profdc9/PicoParanoia/Code/src/fileenc.cpp

/*
 * Copyright (c) 2020 Daniel Marks

This software is provided 'as-is', without any express or implied
warranty. In no event will the authors be held liable for any damages
arising from the use of this software.

Permission is granted to anyone to use this software for any purpose,
including commercial applications, and to alter it and redistribute it
freely, subject to the following restrictions:

1. The origin of this software must not be misrepresented; you must not
   claim that you wrote the original software. If you use this software
   in a product, an acknowledgment in the product documentation would be
   appreciated but is not required.
2. Altered source versions must be plainly marked as such, and must not be
   misrepresented as being the original software.
3. This notice may not be removed or altered from any source distribution.
 */

#include <stdlib.h>
#include <string.h>
#include <stdint.h>
#include <ff.h>
#include <ChaChaPoly.h>
#include "consoleio.h"
#include "fileop.h"
#include "fileenc.h"
#include "keymanager.h"
#include "cryptotool.h"
#include "random.h"

#ifdef __cplusplus
extern "C" {
#endif

int fileenc_check_key_selected(void)
{
  if (current_key_private.entry_type == KEY_TYPE_SYMMETRIC) return 1;
  if (current_key_private.entry_type == KEY_TYPE_ECDH_PRIVATE)
  {
    if (current_key_public.entry_type == KEY_TYPE_ECDH_PUBLIC) return 1;
      else
    {
      file_report_error("No public key selected");
      return 0;
    }
  }
  file_report_error("No private or symmetric key selected");
  return 0;
}

#define FILEENC_READBUF_SIZE (SYMMETRIC_BLOCKLEN*64)

#define FILEENC_WRITEBUF_SIZE 36

// ChaChaPoly::ivSize() returns 8 (the original 64-bit-nonce ChaCha variant),
// not the RFC 8439 96-bit nonce this codebase uses everywhere else -- see
// cryptotool.cpp / third_party/crypto/PROVENANCE.md. This file instantiates
// ChaChaPoly directly (streaming payload cipher, bypassing symmetric_memcrypt)
// so it needs the same explicit wire length.
#define SYMMETRIC_IV_WIRE_LEN 12

typedef struct _fileenc_readbuf
{
  ChaChaPoly *read_cipher;
  FIL read_file;
  uint8_t  read_buf[FILEENC_READBUF_SIZE];
  uint16_t read_filled;
  uint16_t read_curpos;
  FSIZE_t read_progress;
  FIL write_file;
  uint8_t  write_buf[FILEENC_WRITEBUF_SIZE];
  uint16_t write_curpos;  
  fileenc_total_header fth;
} fileenc_state;

int fileenc_base64_readdata(void *v)
{
  fileenc_state *fr = (fileenc_state *)v;
  if (fr->read_curpos >= fr->read_filled)
  {
    UINT br;
    FRESULT res = f_read(&fr->read_file,fr->read_buf,FILEENC_READBUF_SIZE,&br);
    if ((res != FR_OK) || (br == 0)) return -1;
    fr->read_cipher->encrypt(fr->read_buf, fr->read_buf, br);
    fr->read_filled = br;
    fr->read_curpos = 0;
    if ((f_tell(&fr->read_file)-fr->read_progress) >= FILEENC_DISPLAY_INCREMENT)
    {
      console_puts("Reading ");
      console_printuint(f_tell(&fr->read_file));
      console_putch('/');
      console_printuint(f_size(&fr->read_file));
      console_printcrlf();
      fr->read_progress = f_tell(&fr->read_file);
    }
  }
  return fr->read_buf[fr->read_curpos++];
}

int fileenc_base64_writedata(int c, void *v)
{
  fileenc_state *fw = (fileenc_state *)v;

  if (c >= 0)
    fw->write_buf[fw->write_curpos++] = c; 
  if ((fw->write_curpos == FILEENC_WRITEBUF_SIZE) || (c < 0))
  {
    UINT br;
    f_write(&fw->write_file,fw->write_buf,fw->write_curpos,&br);
    f_write(&fw->write_file,"\n",1,&br);
    fw->write_curpos = 0;
  }
  return 0;   // PicoParanoia fix: the ParanoiaBox original omits this return.
              // Same class of bug as fileblockencode_writedata (see fileop.cpp):
              // the caller, base64_encode, ignores the value, but a missing
              // return in a non-void function is UB that HardFaults on this
              // toolchain/target. Caught by -Werror=return-type.
}

const char *fileenc_filename(const char *c)
{
  const char *d = &c[strlen_n(c)];
  while (d>c)
  {
    d--;
    if ((*d == '/') || (*d == ':')) return (d+1);
  }
  return d;
}

void fileenc_encrypt_state(fileenc_state *fs)
{
  char filename_plaintext[256];
  if (!fileenc_check_key_selected()) return;
  {
    char filename_ciphertext[256];
    if (!file_select_plaintext("Select plaintext file", 0, filename_plaintext, sizeof(filename_plaintext)-1)) return;
    if (!file_select_ciphertext("Select directory for ciphertext", 1, filename_ciphertext, sizeof(filename_ciphertext)-1)) return;
    if (!file_enter_filename("Filename for ciphertext output:", filename_ciphertext, sizeof(filename_ciphertext)-1)) return;
    FRESULT fres;
    fres = f_open(&fs->read_file, filename_plaintext, FA_READ);
    if (fres != FR_OK)
    {
      file_report_error("Could not open plaintext file");
      return;
    }
    fres = f_open(&fs->write_file, filename_ciphertext, FA_WRITE | FA_CREATE_NEW);
    if (fres != FR_OK)
    {
      file_report_error("Could not create ciphertext file");
      f_close(&fs->read_file);
      return;    
    }
  }
  console_clrscr();
  console_puts("Encrypting file:\r\n");
  {
    uint8_t secret[KEYMANAGER_MAX_SECRET_LEN];
    uint8_t tag[SYMMETRIC_TAGLEN];
    int secretlen = sizeof(secret);
    uint8_t key_success = 0;

    ChaChaPoly read_cipher;
    uint8_t salt2[KEYMANAGER_HASHLEN];
    uint8_t iv2[SYMMETRIC_IVLEN];
    uint8_t key1[SYMMETRIC_KEYLEN];
    uint8_t key2[SYMMETRIC_KEYLEN];

    memset((void *)&fs->fth,'\000',sizeof(fs->fth));
    randomness_get_whitened_bits(fs->fth.iv1, sizeof(fs->fth.iv1));
    randomness_get_whitened_bits(fs->fth.salt1, sizeof(fs->fth.salt1));
    randomness_get_whitened_bits(salt2, sizeof(salt2));
    randomness_get_whitened_bits(iv2, sizeof(iv2));
 
    if (keymanager_get_symmetric_key(secret, &secretlen))
    {
       randomness_get_whitened_bits(fs->fth.ephemeral_public_key,sizeof(fs->fth.ephemeral_public_key));
       key_success = 1;
    }
    else
    {
       uint8_t ephemeral_private_key[KEYMANAGER_PRIVATEKEY_LEN];
       fileenc_secret_concatenation shared_secrets;
       keymanager_create_ephemeral_key(fs->fth.ephemeral_public_key,sizeof(fs->fth.ephemeral_public_key),
                                       ephemeral_private_key,sizeof(ephemeral_private_key));
       key_success = keymanager_shared_secrets_with_public_key(
          shared_secrets.shared_secret_ephemeral,shared_secrets.shared_secret_private,ephemeral_private_key);
       ctblake2s(secret, secretlen, (const void *)&shared_secrets, sizeof(shared_secrets), NULL, 0);
       memset((void *)&shared_secrets,'\000',sizeof(shared_secrets));
       memset((void *)&ephemeral_private_key,'\000',sizeof(ephemeral_private_key));
    }

    if (key_success)
    {
      key_derivation_function((void *)key1, secret, secretlen, fs->fth.salt1, sizeof(fs->fth.salt1));
      fs->fth.fhpu.fhp.id   =         FILEENC_EXPORT_ID;
      fs->fth.fhpu.fhp.entry_type =   current_key_private.entry_type;
      fs->fth.fhpu.fhp.vers =         FILEENC_EXPORT_VERSION;
      fs->fth.fhpu.fhp.len =          sizeof(fs->fth.fhpu.fhp);
      fs->fth.fhpu.fhp.totallen =     sizeof(fs->fth.fhpu);
      fs->fth.fhpu.fhp.file_length =  f_size(&fs->read_file);
      memcpy((void *)fs->fth.fhpu.fhp.salt2, (void *)salt2, sizeof(fs->fth.fhpu.fhp.salt2));
      memcpy((void *)fs->fth.fhpu.fhp.iv2, (void *)iv2, sizeof(fs->fth.fhpu.fhp.iv2));
      strcpy_n(fs->fth.fhpu.fhp.filename, fileenc_filename(filename_plaintext), sizeof(fs->fth.fhpu.fhp.filename)-1);
      symmetric_memcrypt(1, (void *)key1, (void *)fs->fth.iv1, (void *)fs->fth.tag1, (void *)&fs->fth.fhpu, sizeof(fs->fth.fhpu));
      file_write_block(&fs->write_file, "PARANOIABOX-FILEHEADER", (void *)&fs->fth, sizeof(fs->fth));

      file_write_header(&fs->write_file,"PARANOIABOX-PAYLOAD",0);
      fs->read_cipher = &read_cipher;
      fs->read_filled = fs->read_curpos = 0;
      fs->write_curpos = 0;
      fs->read_progress = 0;
      key_derivation_function((void *)key2, secret, secretlen, salt2, sizeof(salt2));
      fs->read_cipher->setKey((const uint8_t *)key2, fs->read_cipher->keySize());
      fs->read_cipher->setIV((const uint8_t *)iv2, SYMMETRIC_IV_WIRE_LEN);
      base64_encode(fileenc_base64_readdata,(void *)fs,  fileenc_base64_writedata, (void *)fs);
      fileenc_base64_writedata(-1, (void *)fs);
      fs->read_cipher->computeTag((uint8_t *)tag, SYMMETRIC_TAGLEN);
      file_write_header(&fs->write_file,"PARANOIABOX-PAYLOAD",1);
      
      file_write_block(&fs->write_file, "PARANOIABOX-ENDBLOCK", (void *)tag, sizeof(tag));      
    } else file_report_error("Bad secret key");
    memset((void *)&secret,'\000',sizeof(secret));
  }  
  f_close(&fs->write_file);
  f_close(&fs->read_file);
}

void fileenc_encrypt(void)
{
  fileenc_state *fs = (fileenc_state *)malloc(sizeof(fileenc_state));
  if (fs == NULL) return;
  fileenc_encrypt_state(fs);
  free(fs);
}


#define FILEDEC_READBUF_SIZE 512

#define FILEDEC_WRITEBUF_SIZE (SYMMETRIC_BLOCKLEN*64)

typedef struct _filedec_readbuf
{
  FIL          read_file;
  FSIZE_t      read_last_block;
  uint8_t      read_buf[FILEDEC_READBUF_SIZE];
  uint16_t     read_filled;
  uint16_t     read_curpos;
  uint8_t      read_abort;
  FIL          write_file;
  uint8_t      write_buf[FILEDEC_WRITEBUF_SIZE];
  uint16_t     write_curpos; 
  FSIZE_t      write_progress;
  FSIZE_t      write_total;
  ChaChaPoly  *write_cipher;
  fileenc_total_header fth;
} filedec_state;

int filedec_base64_readdata(void *v)
{
  filedec_state *fr = (filedec_state *)v;
  for (;;)
  {
    if (fr->read_curpos >= fr->read_filled)
    {
      UINT br;
      fr->read_last_block = f_tell(&fr->read_file);
      FRESULT res = f_read(&fr->read_file,fr->read_buf,FILEDEC_READBUF_SIZE,&br);
      if ((res != FR_OK) || (br == 0)) return -1;
      fr->read_filled = br;
      fr->read_curpos = 0;
    }
    uint8_t ch = fr->read_buf[fr->read_curpos++];
    if ((ch == '-') || (fr->read_abort))
    {
      f_lseek(&fr->read_file, fr->read_last_block);
      return -1;
    }
    if (is_base64_char(ch)) return ch;
  }
}

int filedec_base64_writedata(int c, void *v)
{
  filedec_state *fw = (filedec_state *)v;

  if (c >= 0) 
    fw->write_buf[fw->write_curpos++] = c; 
  if ((fw->write_curpos == FILEDEC_WRITEBUF_SIZE) || (c < 0))
  {
    UINT br;
    fw->write_cipher->decrypt(fw->write_buf, fw->write_buf, fw->write_curpos);
    f_write(&fw->write_file,fw->write_buf,fw->write_curpos,&br);
    fw->write_curpos = 0;
    if ((f_tell(&fw->write_file)-fw->write_progress) >= FILEENC_DISPLAY_INCREMENT)
    {
      console_puts("Writing ");
      console_printuint(fw->write_progress);
      console_putch('/');
      console_printuint(fw->write_total);
      console_printcrlf();
      fw->write_progress = f_tell(&fw->write_file);
      if (fw->write_progress > fw->fth.fhpu.fhp.file_length)
        fw->read_abort = 1;
    }
  }
  return 0;
}

void fileenc_decrypt_state(filedec_state *fs)
{
  FSIZE_t destroy_output = 0;
  if (!fileenc_check_key_selected()) return;
  {
    char filename_ciphertext[256];
    char filename_plaintext[256];
    if (!file_select_ciphertext("Select ciphertext file", 0, filename_ciphertext, sizeof(filename_ciphertext)-1)) return;
    if (!file_select_plaintext("Select directory for plaintext", 1, filename_plaintext, sizeof(filename_plaintext)-1)) return;
    if (!file_enter_filename("Filename for plaintext output:", filename_plaintext, sizeof(filename_plaintext)-1)) return;
    FRESULT fres;
    fres = f_open(&fs->read_file, filename_ciphertext, FA_READ);
    if (fres != FR_OK)
    {
      file_report_error("Could not open ciphertext file");
      return;
    }
    fres = f_open(&fs->write_file, filename_plaintext, FA_WRITE | FA_CREATE_NEW);
    if (fres != FR_OK)
    {
      file_report_error("Could not create plaintext file");
      f_close(&fs->read_file);
      return;    
    } 
  }
  console_clrscr();
  console_puts("Decrypting file:\r\n");
  {
    uint8_t secret[KEYMANAGER_MAX_SECRET_LEN];
    int secretlen = sizeof(secret);
    uint8_t key_success = 0;

    memset((void *)&fs->fth,'\000',sizeof(fs->fth));
      
    if(file_read_block(&fs->read_file, "PARANOIABOX-FILEHEADER", (void *)&fs->fth, sizeof(fs->fth)))
    {
      uint8_t key1[SYMMETRIC_KEYLEN];

    if (keymanager_get_symmetric_key(secret, &secretlen))
       key_success = 1;
    else
    {
       fileenc_secret_concatenation shared_secrets;
       key_success = keymanager_shared_secrets_with_private_key(
          shared_secrets.shared_secret_ephemeral,shared_secrets.shared_secret_private,fs->fth.ephemeral_public_key);
       ctblake2s(secret, secretlen, (const void *)&shared_secrets, sizeof(shared_secrets), NULL, 0);
       memset((void *)&shared_secrets,'\000',sizeof(shared_secrets));
    }
    
     if (key_success)
     {
        key_derivation_function((void *)key1, secret, secretlen, fs->fth.salt1, sizeof(fs->fth.salt1));
        if (symmetric_memcrypt(0, (void *)key1, (void *)fs->fth.iv1, (void *)fs->fth.tag1, (void *)&fs->fth.fhpu, sizeof(fs->fth.fhpu)))
        {
           if ((fs->fth.fhpu.fhp.id == FILEENC_EXPORT_ID) && (fs->fth.fhpu.fhp.vers == FILEENC_EXPORT_VERSION) &&
               (fs->fth.fhpu.fhp.len == sizeof(fs->fth.fhpu.fhp)) && (fs->fth.fhpu.fhp.entry_type == current_key_private.entry_type))
           {
              fs->fth.fhpu.fhp.filename[sizeof(fs->fth.fhpu.fhp.filename)-1] = '\000';
              if (file_skip_header(&fs->read_file,"PARANOIABOX-PAYLOAD",0))
              {
                ChaChaPoly  write_cipher;
                uint8_t key2[SYMMETRIC_KEYLEN];
                key_derivation_function((void *)key2, secret, secretlen, fs->fth.fhpu.fhp.salt2, sizeof(fs->fth.fhpu.fhp.salt2));
                fs->write_cipher = &write_cipher;
                fs->read_filled = fs->read_curpos = 0;
                fs->read_abort = 0;
                fs->write_curpos = 0;
                fs->write_progress = 0;
                fs->write_total = fs->fth.fhpu.fhp.file_length;
                fs->write_cipher->setKey((const uint8_t *)key2, fs->write_cipher->keySize());
                fs->write_cipher->setIV((const uint8_t *)fs->fth.fhpu.fhp.iv2, SYMMETRIC_IV_WIRE_LEN);
                base64_decode(filedec_base64_readdata,(void *)fs,  filedec_base64_writedata, (void *)fs);
                filedec_base64_writedata(-1, (void *)fs);
                if (f_tell(&fs->write_file) == fs->fth.fhpu.fhp.file_length)
                {
                  if (file_skip_header(&fs->read_file,"PARANOIABOX-PAYLOAD",1))
                  {
                    uint8_t tag[SYMMETRIC_TAGLEN];
                    if(file_read_block(&fs->read_file, "PARANOIABOX-ENDBLOCK", (void *)tag, sizeof(tag)))
                    {
                      if (fs->write_cipher->checkTag(tag, SYMMETRIC_TAGLEN))
                      {
                         destroy_output = fs->fth.fhpu.fhp.file_length;
                      }
                      else file_report_error("Payload Tag is invalid");
                    } else file_report_error("End block not found");
                  } else file_report_error("End of payload not found");                
                } else file_report_error("Payload length does not match header");
              } else file_report_error("No payload found");
           } else file_report_error("Wrong version of header");
        } else file_report_error("Header Tag is invalid");
      } else file_report_error("Could not read file header");
    } else file_report_error("Bad secret key");
    memset((void *)&secret,'\000',sizeof(secret));
  }
  f_lseek(&fs->write_file,destroy_output);
  f_truncate(&fs->write_file);
  f_close(&fs->write_file);
  f_close(&fs->read_file);
}

void fileenc_decrypt(void)
{
  filedec_state *fs = (filedec_state *)malloc(sizeof(filedec_state));
  if (fs == NULL) return;
  fileenc_decrypt_state(fs);
  free(fs);
}

#ifdef __cplusplus
}
#endif  
