profdc9/PicoParanoia/Code/src/TNTSCAnsi.cpp

/* 
  Copyright (C) 2007 by Daniel Marks

  This software is provided 'as-is', without any express or implied
  warranty.  In no event will the authors be held liable for any damages
  arising from the use of this software.

  Permission is granted to anyone to use this software for any purpose,
  including commercial applications, and to alter it and redistribute it
  freely, subject to the following restrictions:

  1. The origin of this software must not be misrepresented; you must not
     claim that you wrote the original software. If you use this software
     in a product, an acknowledgment in the product documentation would be
     appreciated but is not required.
  2. Altered source versions must be plainly marked as such, and must not be
     misrepresented as being the original software.
  3. This notice may not be removed or altered from any source distribution.
  
  Daniel L. Marks profdc9@gmail.com

*/

#include <stdio.h>
#include <stdlib.h>

#include "TNTSCAnsi.h"

#define STRICT_VT100

#define memmove vidmemmove

static void *vidmemmove(void *s1, const void *s2, size_t n)
{
	unsigned char *ss1 = (unsigned char *)s1;
	const unsigned char *ss2 = (const unsigned char *)s2;
	if (ss1 > ss2) {
		ss1 += n;
		ss2 += n;
		while (n-- > 0) *(--ss1) = *(--ss2);
	} else {
		while (n-- > 0) *ss1++ = *ss2++;
	}
	return s1;
}

// Optional per-cell change hook. A host project can define
// TNTSCANSI_CELL_CHANGED(cur, index, ch) (via the auto-included tntscansi_hook.h)
// to be notified with the linear buffer index whenever a cell changes value, so
// it can blit just that cell. Default is a no-op, which keeps this file a
// standalone VT100 text-buffer emulator with unchanged behavior.
#if defined(__has_include)
#  if __has_include("tntscansi_hook.h")
#    include "tntscansi_hook.h"
#  endif
#endif
#ifndef TNTSCANSI_CELL_CHANGED
#define TNTSCANSI_CELL_CHANGED(cur, index, ch) ((void)0)
#endif

// Optional whole-region clear hook. clear_region() fires this once for the
// whole span instead of the per-cell hook, so a host can do one fast solid
// fill (e.g. pico_ntsc_clear_span) instead of one glyph-blit per cell. Default
// is a no-op.
#ifndef TNTSCANSI_REGION_CLEARED
#define TNTSCANSI_REGION_CLEARED(cur, y1, x1, y2, x2, reverse) ((void)0)
#endif

// Write one cell and notify the hook with its linear index into cur.data.
#define VS_PUT(cur, ptr, val) do {                                  \
    screenchartype *vp_ = (ptr);                                    \
    screenchartype vv_ = (screenchartype)(val);                     \
    *vp_ = vv_;                                                      \
    TNTSCANSI_CELL_CHANGED((cur), (int)(vp_ - (cur).data), vv_);     \
} while (0)

void TNTSCAnsi_class::begin(void *buf, int rows, int columns)
{
  cur.data = (screenchartype *)buf;
  cur.bottom_scroll = cur.rows = rows;
  cur.columns = columns;
  cur.cur_ansi_number = cur.top_scroll = 0;
  cur.ansi_elements = cur.ansi_reading_number = 0;
  cur.next_char_send = &TNTSCAnsi_class::std_interpret_char;
  cur.old_attrib = cur.attrib = 0x07;
  clear_region(0,0,rows-1,columns-1,cur.attrib);
  cur.xpos = cur.ypos = cur.old_xpos = cur.old_ypos = 0;
  cur.xpos_cursor = cur.ypos_cursor = NULL;
}

void TNTSCAnsi_class::end()
{
}

void TNTSCAnsi_class::clear_region(int y1, int x1, int y2, int x2, int atrb)
{
  screenchartype *ch = loc_in_virtscreen(cur,y1,x1);
  screenchartype *tr = loc_in_virtscreen(cur,y2,x2);
#ifdef VTATTRIB
  int clr_with = (atrb << 8) | 0x20;
#else
  // Same reverse-video bit packing as change_character() ((attrib & 0x08) << 4
  // -> bit 7), so a clear while highlighted fills with reverse-video blanks
  // instead of always plain ones.
  int clr_with = 0x20 | ((atrb & 0x08) << 4);
#endif

  // Update the virtscreen buffer directly (no per-cell hook): the framebuffer
  // gets one fast solid fill below instead of one glyph-blit per cell.
  while (ch<=tr) *ch++ = (screenchartype)clr_with;
  TNTSCANSI_REGION_CLEARED(cur, y1, x1, y2, x2, (clr_with & 0x80) != 0);
}

void TNTSCAnsi_class::clear_virtscreen(int mode)
{
  switch (mode)
  {
    case 0:  clear_region(cur.ypos,cur.xpos,cur.rows-1,cur.columns-1,cur.attrib);
             break;
    case 1:  clear_region(0,0,cur.ypos,cur.xpos,cur.attrib);
             break;
    default: clear_region(0,0,cur.rows-1,cur.columns-1,cur.attrib);
             cur.xpos = cur.ypos = 0;
             break;
  }
}

void TNTSCAnsi_class::clear_to_eol(int mode)
{
  switch(mode)
    {
      case 0: clear_region(cur.ypos,cur.xpos,cur.ypos,cur.columns-1,cur.attrib);
              break;
      case 1: clear_region(cur.ypos,0,cur.ypos,cur.xpos,cur.attrib);
              break;
      default: clear_region(cur.ypos,0,cur.ypos,cur.columns-1,cur.attrib);
	}
}

void TNTSCAnsi_class::move_cursor()
{
	if (cur.xpos_cursor != NULL) *cur.xpos_cursor = cur.xpos;
	if (cur.ypos_cursor != NULL) *cur.ypos_cursor = cur.ypos;
}

void TNTSCAnsi_class::position_console(int ypos, int xpos, int rel)
{
  if (rel)
    {
      cur.xpos += xpos;
      cur.ypos += ypos;
  } else
    {
      cur.xpos = xpos;
      cur.ypos = ypos;
    }
  if (cur.xpos < 0) cur.xpos = 0;
  if (cur.xpos >= cur.columns) cur.xpos = cur.columns-1;
  if (cur.ypos < 0) cur.ypos = 0;
  if (cur.ypos >= cur.rows) cur.ypos = cur.rows-1;
  move_cursor();
}

void TNTSCAnsi_class::delete_chars_in_line(int char_move)
{
   screenchartype *next_move;
   screenchartype *end_move;
   screenchartype *start_move;
   screenchartype clr_with;

#ifdef VTATTRIB
   clr_with = (cur.attrib << 8) | 0x20;
#else
   clr_with = 0x20;
#endif
   start_move = loc_in_virtscreen(cur,cur.ypos,cur.xpos);
   end_move = loc_in_virtscreen(cur,cur.ypos,cur.columns);
   if ((cur.xpos + char_move) < cur.columns)
   {
     next_move = loc_in_virtscreen(cur,cur.ypos,cur.xpos+char_move);
     while (next_move<end_move) { VS_PUT(cur, start_move, *next_move); start_move++; next_move++; }
   }
   while (start_move<end_move) { VS_PUT(cur, start_move, clr_with); start_move++; }
}

void TNTSCAnsi_class::scroll_virt_up_at_cursor(int dir)
{
   screenchartype clr_with;
   screenchartype *beginScr;
   screenchartype *endofScr;
   screenchartype *lastLine;
   screenchartype *nextLine;
   unsigned int real_scroll_length;

   if ((cur.ypos >= cur.top_scroll) &&
       (cur.ypos < cur.bottom_scroll))
   {
 #ifdef VTATTRIB
	 int clr_with = (cur.attrib << 8) | 0x20;
 #else
	 int clr_with = 0x20;
 #endif
     beginScr = loc_in_virtscreen(cur,cur.ypos,0);
     endofScr = loc_in_virtscreen(cur,cur.bottom_scroll,0);
     lastLine = endofScr - cur.columns;
     nextLine = beginScr + cur.columns;
     real_scroll_length = ((unsigned int) lastLine) -
                          ((unsigned int) beginScr);

     if (dir)
       {
	 for (unsigned int k=0;k<real_scroll_length;k++) VS_PUT(cur, beginScr+k, nextLine[k]);
         while (lastLine < endofScr) { VS_PUT(cur, lastLine, clr_with); lastLine++; }
       } else
	 {
	   for (int k=(int)real_scroll_length-1;k>=0;k--) VS_PUT(cur, nextLine+k, beginScr[k]);
           while (beginScr < nextLine) { VS_PUT(cur, beginScr, clr_with); beginScr++; }
	 }
   }
}

void TNTSCAnsi_class::scroll_virtscreen()
 {
#ifdef VTATTRIB
   int clr_with = (cur.attrib << 8) | 0x20;
#else
   int clr_with = 0x20;
#endif
   screenchartype *beginScr = loc_in_virtscreen(cur,cur.top_scroll,0);
   screenchartype *endofScr = loc_in_virtscreen(cur,cur.bottom_scroll,0);
   screenchartype *lastLine = endofScr - cur.columns;
   screenchartype *nextLine = beginScr + cur.columns;
   unsigned int real_scroll_length = ((unsigned int) lastLine) -
                          ((unsigned int) beginScr);
   for (unsigned int k=0;k<real_scroll_length;k++) VS_PUT(cur, beginScr+k, nextLine[k]);
   while (lastLine < endofScr) { VS_PUT(cur, lastLine, clr_with); lastLine++; }
 };

void TNTSCAnsi_class::set_scroll_region(int low, int high)
{
   low--;
   high = (high >= cur.rows) ? cur.rows : high;
   low = (low < 0) ? 0 : low;

   cur.top_scroll = low;
   cur.bottom_scroll = high;
}

void TNTSCAnsi_class::change_attribute(int attrib)
{
  cur.attrib = attrib;
}

void TNTSCAnsi_class::change_character(int ch)
{
#ifdef VTATTRIB
  VS_PUT(cur, loc_in_virtscreen(cur,cur.ypos,cur.xpos), ch | (cur.attrib << 8));
#else
  VS_PUT(cur, loc_in_virtscreen(cur,cur.ypos,cur.xpos), ch | ((cur.attrib & 0x08) << 4));
#endif
}

void TNTSCAnsi_class::special_ansi_charset_0(unsigned char ch)
{
  cur.next_char_send = &TNTSCAnsi_class::std_interpret_char;
}

void TNTSCAnsi_class::special_ansi_charset_1(unsigned char ch)
{
  cur.next_char_send = &TNTSCAnsi_class::std_interpret_char;
}

void TNTSCAnsi_class::std_interpret_ansi(unsigned char ch)
{
  switch (ch)
  {
    case '(':  cur.next_char_send = &TNTSCAnsi_class::special_ansi_charset_0;
               return;
    case ')':  cur.next_char_send = &TNTSCAnsi_class::special_ansi_charset_1;
               return;
    case '[':  cur.cur_ansi_number = 0;
               cur.ansi_elements = 0;
               cur.ansi_reading_number = 0;
               cur.next_char_send = &TNTSCAnsi_class::special_reading_ansi;
               return;
    case '7':  cur.old_attrib = cur.attrib;
               cur.old_xpos = cur.xpos;
               cur.old_ypos = cur.ypos;
               break;
    case '8':  change_attribute(cur.old_attrib);
               position_console(cur.ypos,cur.xpos,0);
               break;
    case 'E':  cur.xpos = 0;
    case 'D':  cur.ypos++;
               if (cur.ypos >= cur.bottom_scroll)
               {
                 scroll_virtscreen();
                 cur.ypos--;
               }
               move_cursor();
               break; 
    case 'M':  cur.ypos--;
               if (cur.ypos < cur.top_scroll)
               {
                 cur.ypos++;
                 scroll_virt_up_at_cursor(0);
               }
               move_cursor();
               break;    /* recalculate screen pos */
  }
  if (ch != 27)
    cur.next_char_send = &TNTSCAnsi_class::std_interpret_char;
}

void TNTSCAnsi_class::std_interpret_char(unsigned char ch)
{
  switch (ch)
  {
    case 27: cur.next_char_send = &TNTSCAnsi_class::std_interpret_ansi;
             return;
    case 12: clear_virtscreen(2);
             break;
    case 13: cur.xpos = 0;        /* return = back to begin */
             break;
    case 10: cur.ypos++;
             if (cur.ypos >= cur.bottom_scroll)
                     /* if we're at bottom */
             {
               if (cur.ypos == cur.bottom_scroll)
			         scroll_virtscreen();        /* and scroll it! */
               cur.ypos--;            /* go back up a line */
             }
             break;  
    case 9:  position_console(cur.ypos,cur.xpos+(8-(cur.xpos % 8)),0);
             break;
    case 8:  cur.xpos--;               /* backspace on screen */
             if (cur.xpos<0)
             {
               cur.xpos = cur.columns - 1;
               cur.ypos--;
               if (cur.ypos<0)
				  cur.ypos=0;
             }
             break;
    default: if (!ch)
                break;
             change_character(ch);
             cur.xpos++;
             if (cur.xpos >= cur.columns)
	       {
#ifdef STRICT_VT100
		 cur.xpos = cur.columns-1;
#else
		 cur.xpos = 0;
                 cur.ypos++;
                 if (cur.ypos == cur.bottom_scroll)
		   {
		     cur.ypos--;
		     scroll_virtscreen();
		   }
#endif
	       }
             break;
    }
  move_cursor();
}

void TNTSCAnsi_class::special_reading_ansi(unsigned char ch)
{
  if ((ch>='0') && (ch<='9'))
  {
    cur.cur_ansi_number = (cur.cur_ansi_number * 10) + (ch - '0');
    cur.ansi_reading_number = 1;
    return;
  }

  if ((cur.ansi_reading_number) || (ch == ';'))
  {
     if (cur.ansi_elements<MAX_ANSI_ELEMENTS)
      cur.ansi_element[cur.ansi_elements++] = cur.cur_ansi_number;
     cur.ansi_reading_number = 0;
  }
  cur.cur_ansi_number = 0;
  switch (ch)
  {
    case '?':
    case ';':   return;
    case 'D':   position_console(0,(cur.ansi_elements) ?
			 -cur.ansi_element[0] : -1,1);
                break;
    case 'a':
    case 'C':   position_console(0,(cur.ansi_elements) ?
			 cur.ansi_element[0] : 1,1);
                break;
    case 'A':   position_console((cur.ansi_elements) ? 
		         -cur.ansi_element[0] : -1,0,1);
                break;
    case 'e':
    case 'B':   position_console((cur.ansi_elements) ?
			 cur.ansi_element[0] : 1,0,1);
                break;
    case '`':
    case 'G':   
                {
                  int temp = cur.ansi_elements ? cur.ansi_element[0] : 1;
		  if (temp)
		    temp--;
                  position_console(cur.ypos,temp,0);
		}
                break;
    case 'E':   position_console(cur.ypos + 
		         ((cur.ansi_elements) ? cur.ansi_element[0] : 1),
			 0,0);
                break;
    case 'F':   position_console(cur.ypos - 
		         ((cur.ansi_elements) ? cur.ansi_element[0] : 1),
			 0,0);
                break;
    case 'd':   
                {
                  int temp = cur.ansi_elements ? cur.ansi_element[0] : 1;
		  if (temp)
		    temp--;
                  position_console(temp,cur.xpos,0);
		}
                break;
    case 'f':
    case 'H':
      {
        int row = (cur.ansi_elements > 0) ? cur.ansi_element[0] : 1;
        int col = (cur.ansi_elements > 1) ? cur.ansi_element[1] : 1;
	if (row)
	  row--;
	if (col)
	  col--;
        position_console(row,col,0);
      }
      break;
    case 'J':   clear_virtscreen((cur.ansi_elements) ?
		       cur.ansi_element[0]: 0);
                break;
    case 'L':   {
                  int lines = (cur.ansi_elements) ? 
		     cur.ansi_element[0] : 1;
                  while (lines>0)
                  {
                    scroll_virt_up_at_cursor(0);
                    lines--;
                  }
                }
                break;
    case 'M':   {
                  int lines = (cur.ansi_elements) ? 
		     cur.ansi_element[0] : 1;
                  while (lines>0)
                  {
                    scroll_virt_up_at_cursor(1);
                    lines--;
                  }
                }
                break;
    case 'P':   delete_chars_in_line((cur.ansi_elements) ? 
			 cur.ansi_element[0] : 1);
                break;
    case 'K':   clear_to_eol(cur.ansi_elements ? 
		    cur.ansi_element[0] : 0);
                break;
    case 's':   cur.old_xpos = cur.xpos;
                cur.old_ypos = cur.ypos;
                break;
    case 'u':   position_console(cur.old_ypos,cur.old_xpos,0);
                break;
    case 'r':   {
                  int low = (cur.ansi_elements > 0) ?
		      cur.ansi_element[0] : 1;
                  int high = (cur.ansi_elements > 1) ?
		      cur.ansi_element[1] : cur.rows;
                  if (low<=high)
                    set_scroll_region(low,high);
                }
                break;
    case 'm':
       {
          int count = 0;
          int cthing;
          if (!cur.ansi_elements)
            change_attribute(0x07);
          while (count < cur.ansi_elements)
          {
            cthing = cur.ansi_element[count];
            switch (cthing)
            {
              case 0:
              case 27: change_attribute(0x07);
                       break;
              case 1:  change_attribute(cur.attrib | 0x08);
                       break;
              case 5:  change_attribute(cur.attrib | 0x80);
                       break;
              case 7:  change_attribute(0x70);
                       break;
              case 21:
              case 22: change_attribute(cur.attrib & 0xF7);
                       break;
              case 25: change_attribute(cur.attrib & 0x7F);
                       break;
              default:
                if ((cthing>=30) && (cthing<=37))
		  {
		    change_attribute((cur.attrib & 0xF8) | (cthing-30));
		  }
                if ((cthing>=40) && (cthing<=47))
		  {
		    change_attribute((cur.attrib & 0x8F) | 
				     ((cthing-40) << 4));
		  }
                break;
	      }
            count++;
	  }
	}
      break;
      
  }
  cur.next_char_send = &TNTSCAnsi_class::std_interpret_char;
}

void TNTSCAnsi_class::output_character(unsigned char ch)
{
   ((*this).*(cur.next_char_send))(ch);
}

void TNTSCAnsi_class::set_cursor_ptr(unsigned short *xpos, unsigned short *ypos)
{
  cur.xpos_cursor = xpos;
  cur.ypos_cursor = ypos;
}


TNTSCAnsi_class TNTSCAnsi;
